KiranGunathilaka/gaurdian-call-IoT/Assets/OtherImages/20240525_033147.jpg

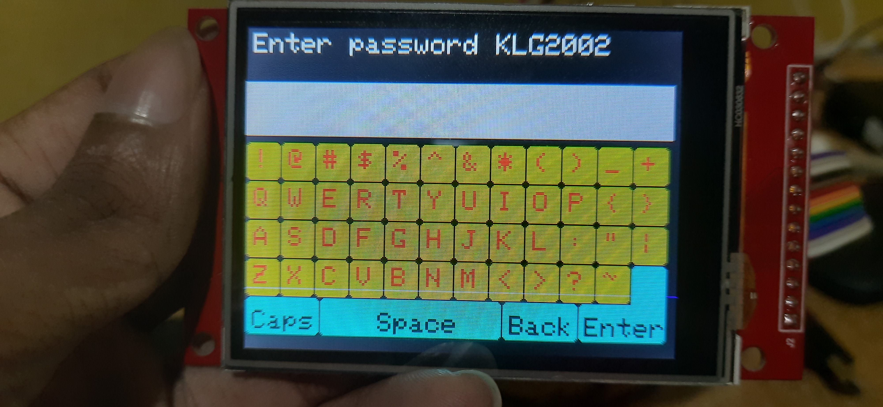
Assets/OtherImages/20240525_033147.jpg
