KiranGunathilaka/gaurdian-call-IoT/Assets/OtherImages/20240525_033200.jpg

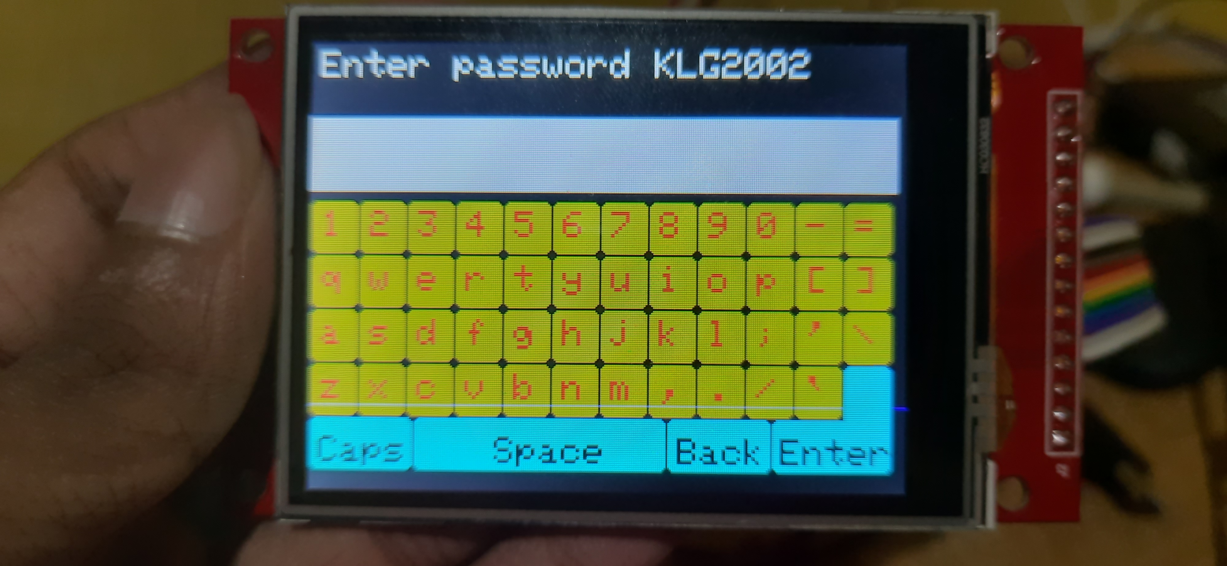
Assets/OtherImages/20240525_033200.jpg
