KiranGunathilaka/gaurdian-call-IoT/Assets/OtherImages/20240613_105201.jpg

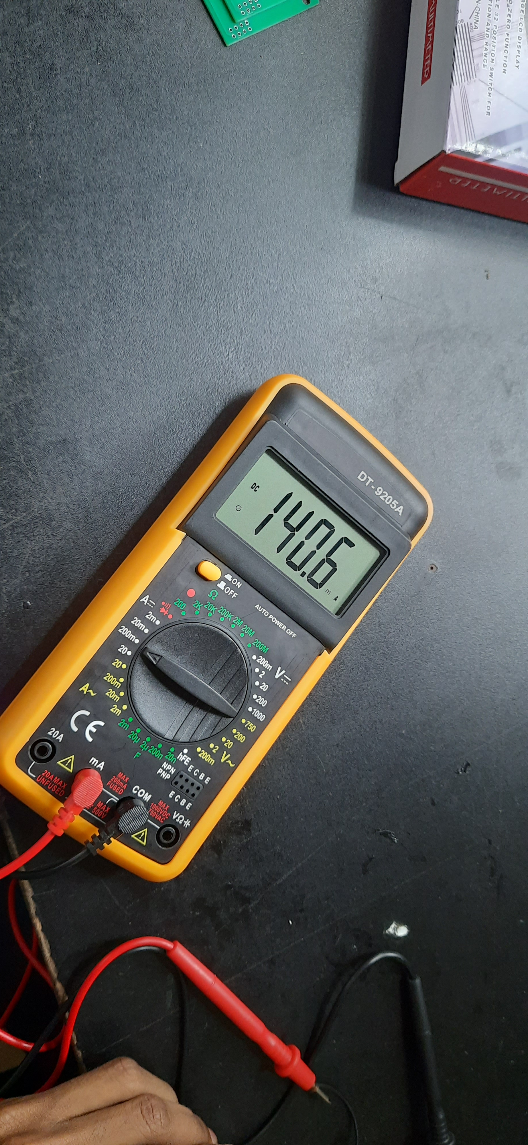
Assets/OtherImages/20240613_105201.jpg
