KiranGunathilaka/gaurdian-call-IoT/Assets/OtherImages/20240613_105238.jpg

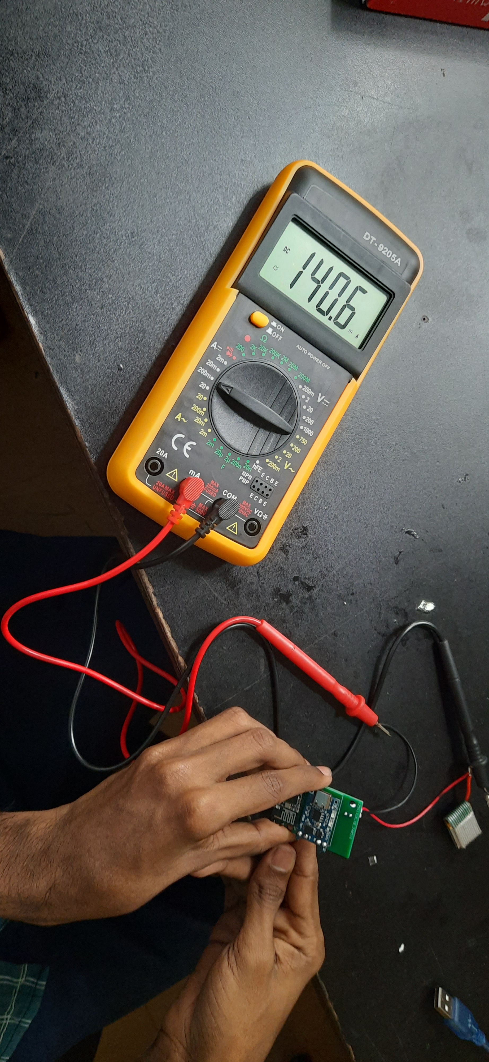
Assets/OtherImages/20240613_105238.jpg
