KiranGunathilaka/gaurdian-call-IoT/Assets/OtherImages/20240613_105256.jpg

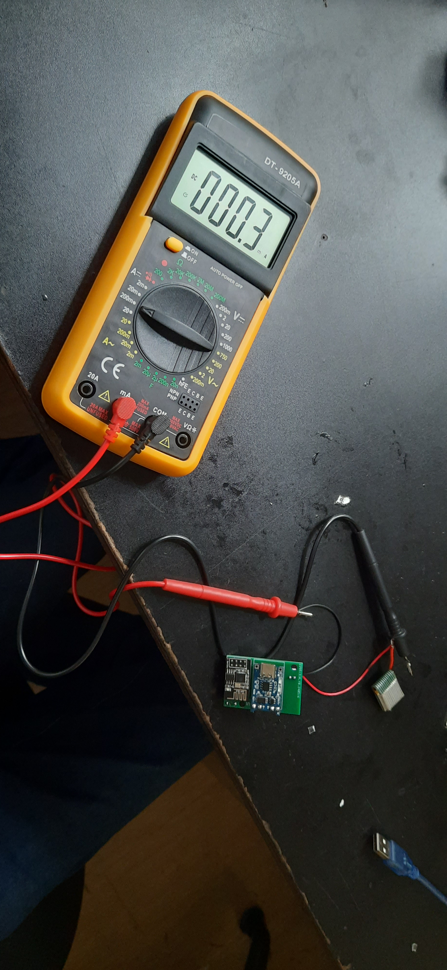
Assets/OtherImages/20240613_105256.jpg
