KiranGunathilaka/gaurdian-call-IoT/Assets/OtherImages/20240613_105300.jpg

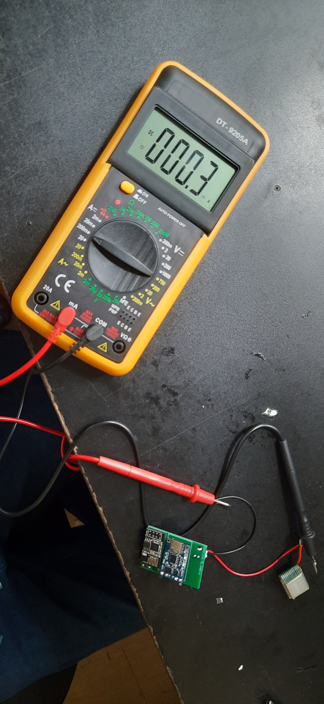
Assets/OtherImages/20240613_105300.jpg
