KiranGunathilaka/gaurdian-call-IoT/Assets/OtherImages/20240613_173540.jpg

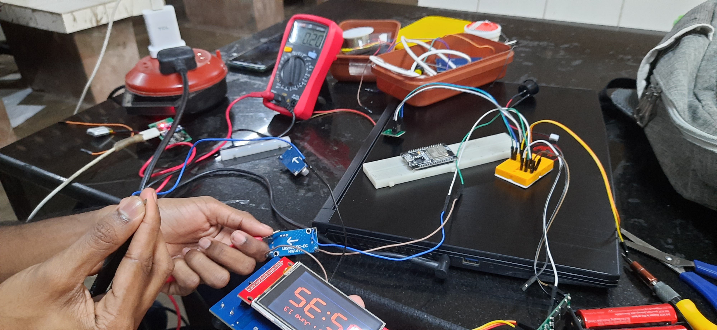
Assets/OtherImages/20240613_173540.jpg
