KiranGunathilaka/gaurdian-call-IoT/Assets/OtherImages/20240613_173549.jpg

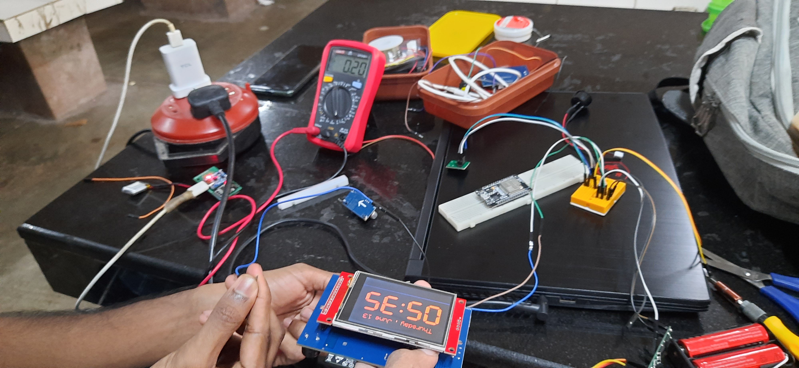
Assets/OtherImages/20240613_173549.jpg
