KiranGunathilaka/gaurdian-call-IoT/Assets/OtherImages/20240614_130550.jpg

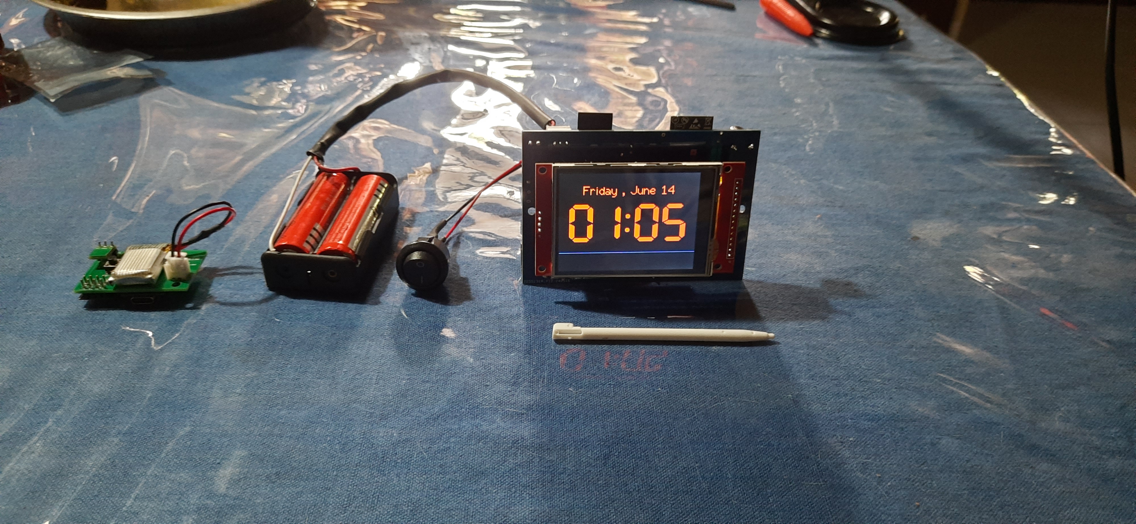
Assets/OtherImages/20240614_130550.jpg
