KiranGunathilaka/gaurdian-call-IoT/Assets/OtherImages/20240614_130608.jpg

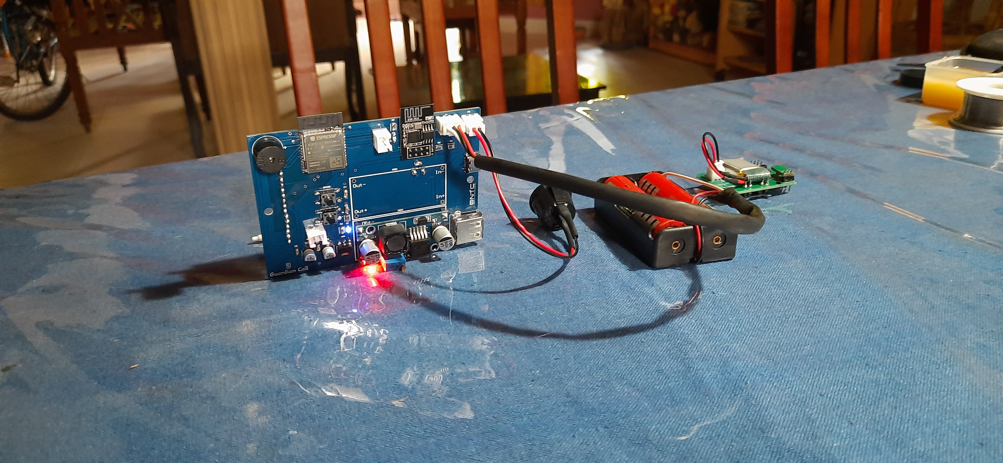
Assets/OtherImages/20240614_130608.jpg
