KiranGunathilaka/gaurdian-call-IoT/Assets/OtherImages/20240614_203509.jpg

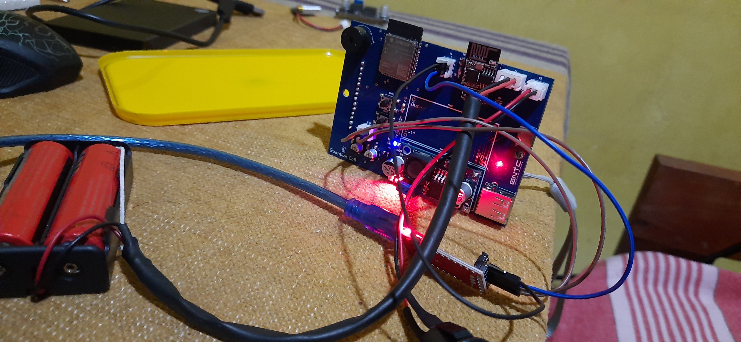
Assets/OtherImages/20240614_203509.jpg
