KiranGunathilaka/gaurdian-call-IoT/Assets/OtherImages/20240614_231927.jpg

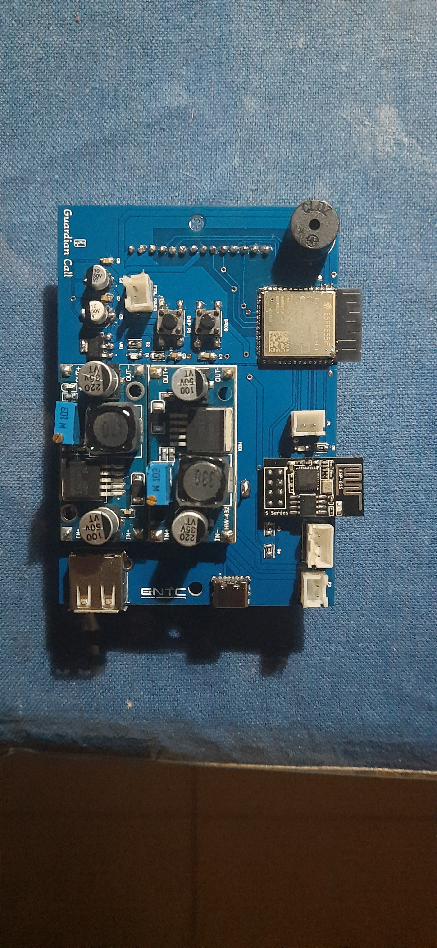
Assets/OtherImages/20240614_231927.jpg
