KiranGunathilaka/gaurdian-call-IoT/Assets/OtherImages/20240614_232202.jpg

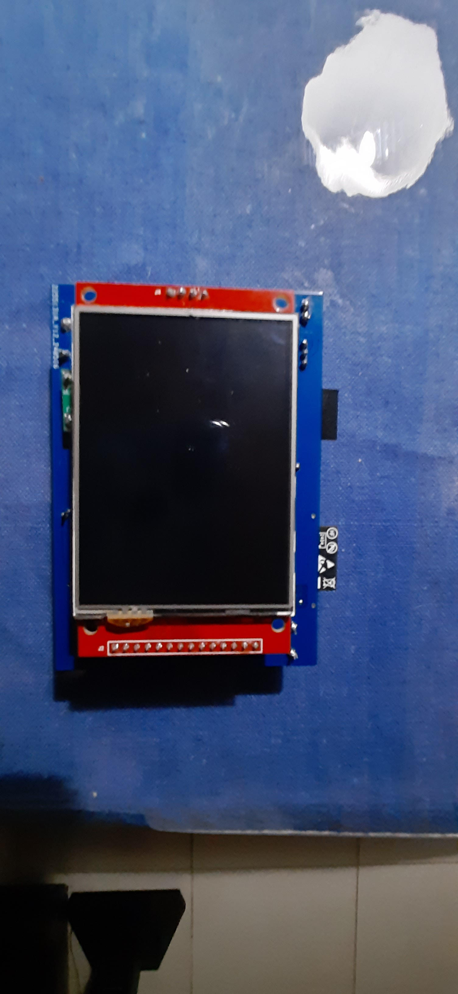
Assets/OtherImages/20240614_232202.jpg
