KiranGunathilaka/gaurdian-call-IoT/Assets/OtherImages/20240614_232258.jpg

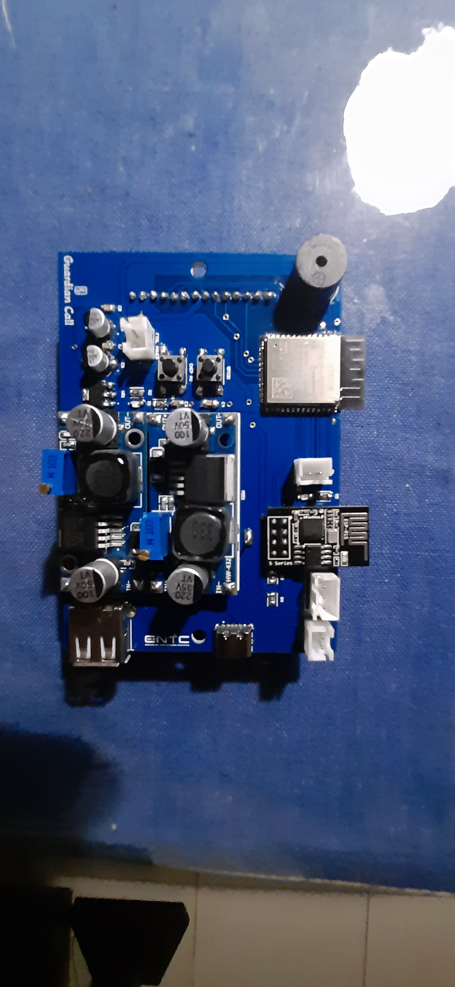
Assets/OtherImages/20240614_232258.jpg
