KiranGunathilaka/gaurdian-call-IoT/Assets/OtherImages/20240614_232338.jpg

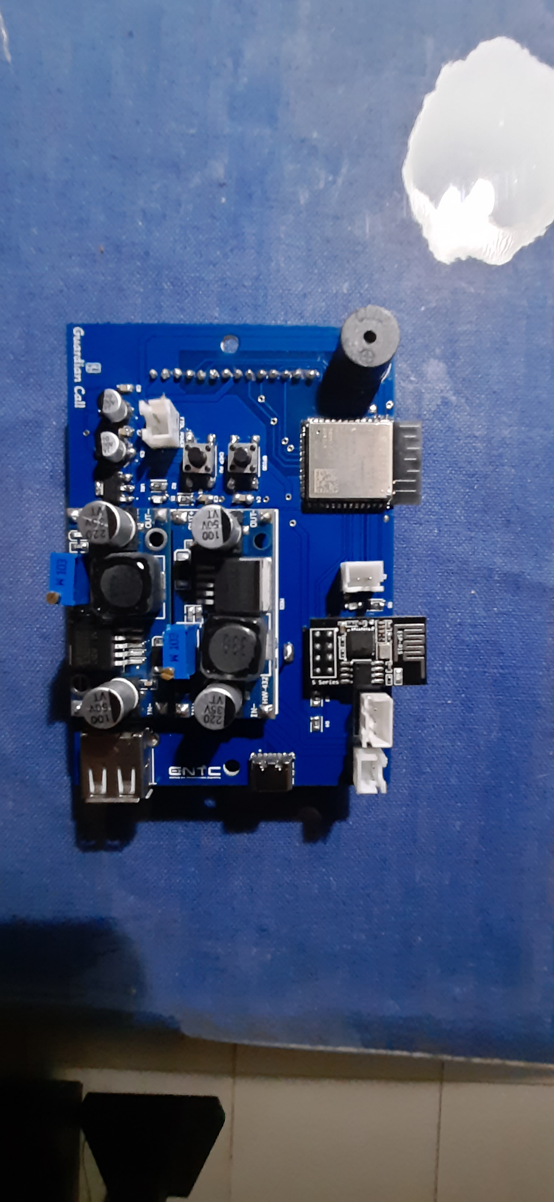
Assets/OtherImages/20240614_232338.jpg
