KiranGunathilaka/gaurdian-call-IoT/Assets/OtherImages/20240614_232511.jpg

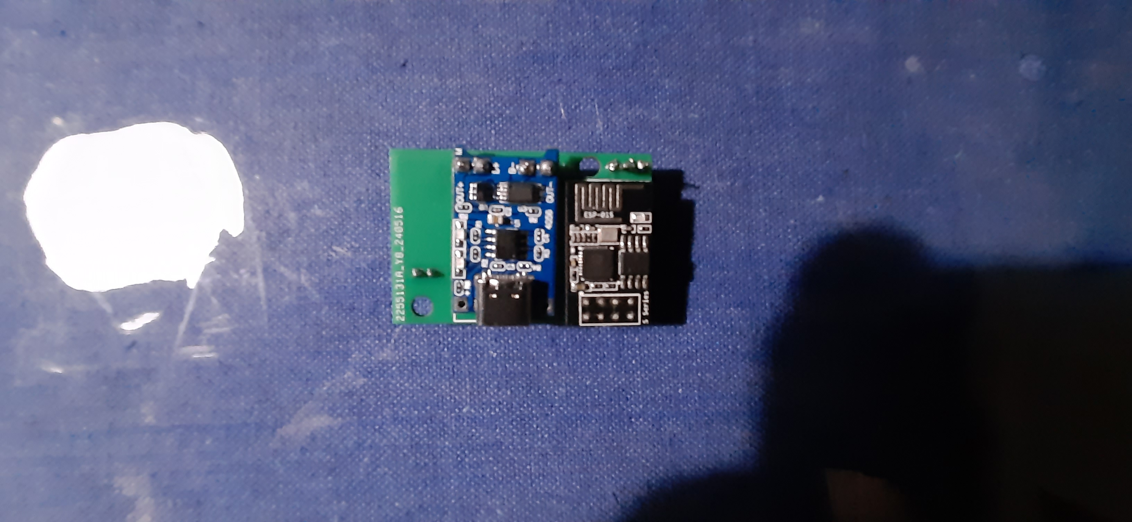
Assets/OtherImages/20240614_232511.jpg
