KiranGunathilaka/gaurdian-call-IoT/Assets/OtherImages/20240614_232523.jpg

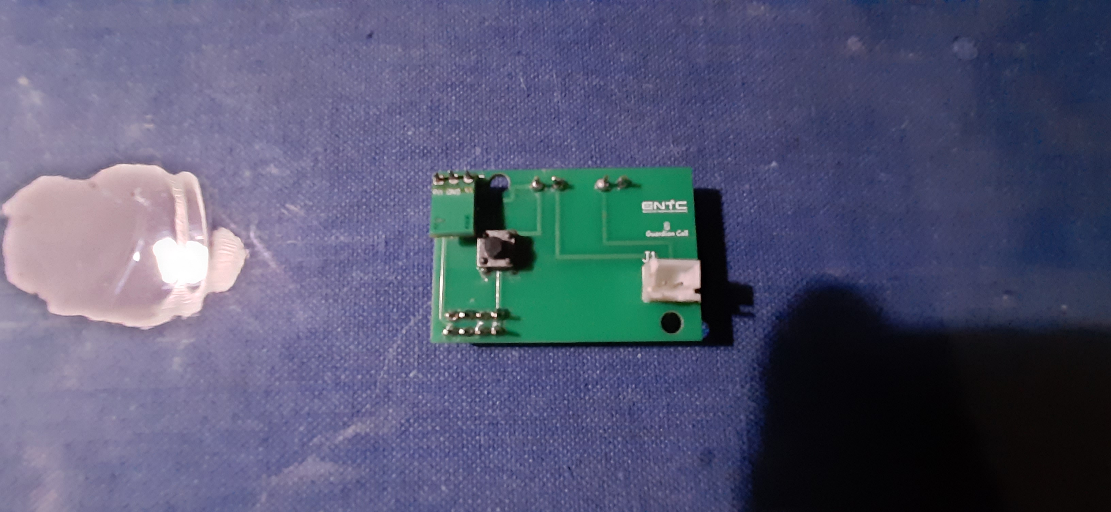
Assets/OtherImages/20240614_232523.jpg
