KiranGunathilaka/gaurdian-call-IoT/Assets/OtherImages/20240614_232553.jpg

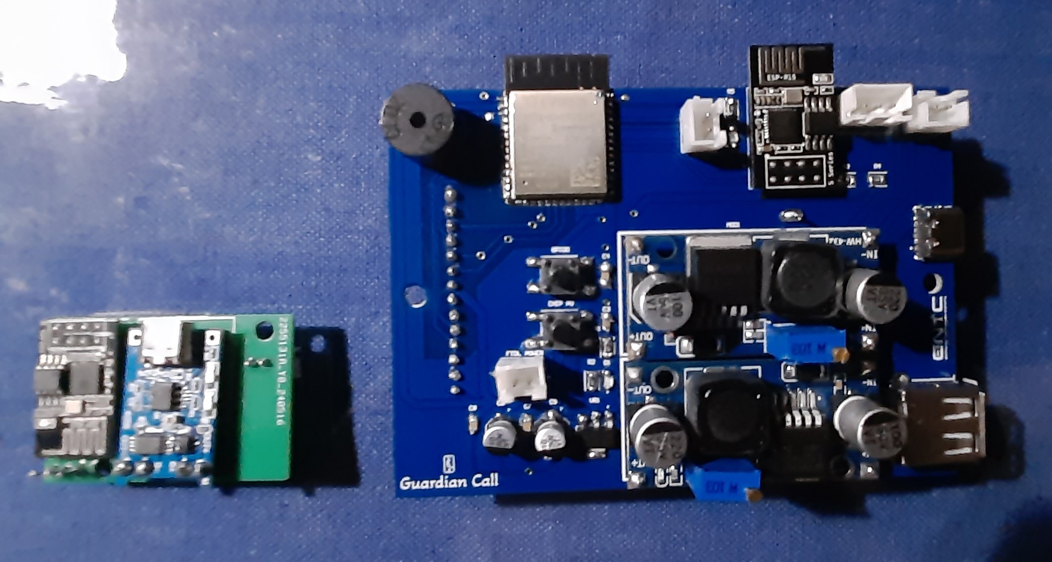
Assets/OtherImages/20240614_232553.jpg
