KiranGunathilaka/gaurdian-call-IoT/Assets/OtherImages/20240614_232625.jpg

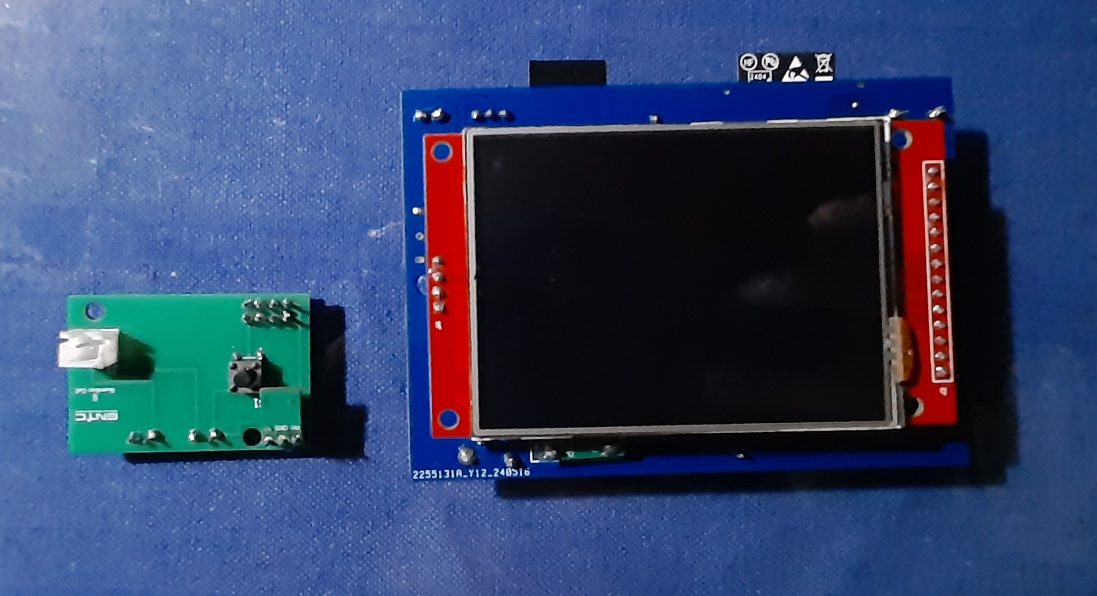
Assets/OtherImages/20240614_232625.jpg
