KiranGunathilaka/gaurdian-call-IoT/Assets/OtherImages/20240630_153155.jpg

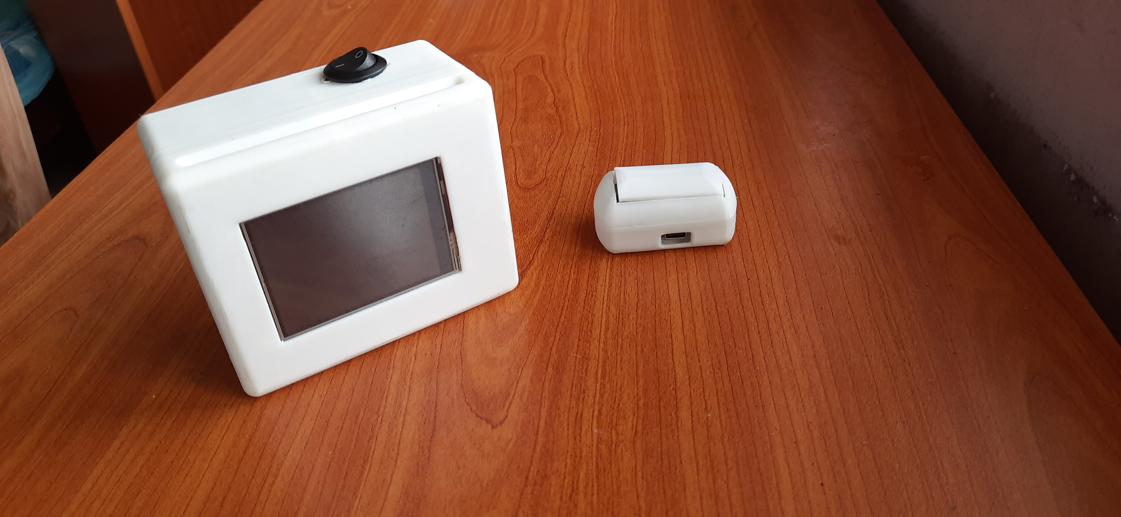
Assets/OtherImages/20240630_153155.jpg
