KiranGunathilaka/gaurdian-call-IoT/Assets/OtherImages/20240630_153201.jpg

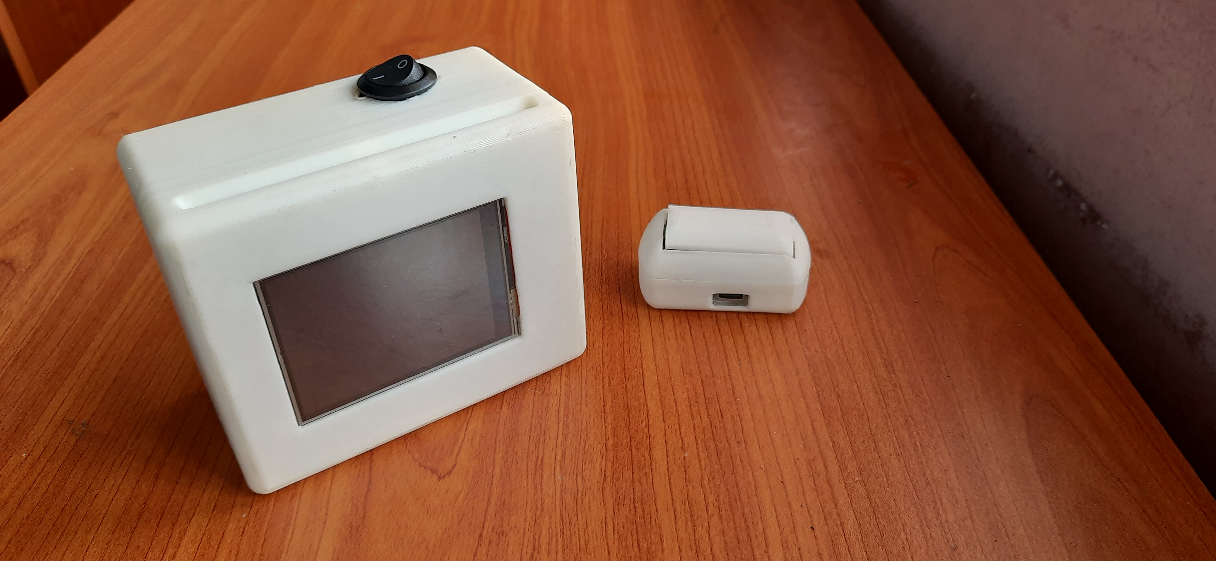
Assets/OtherImages/20240630_153201.jpg
