KiranGunathilaka/gaurdian-call-IoT/Assets/OtherImages/20240703_032037.jpg

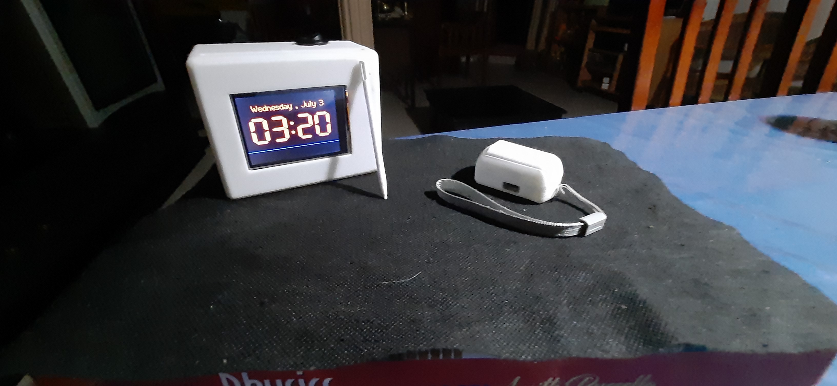
Assets/OtherImages/20240703_032037.jpg
