KiranGunathilaka/gaurdian-call-IoT/Assets/OtherImages/20240703_032049.jpg

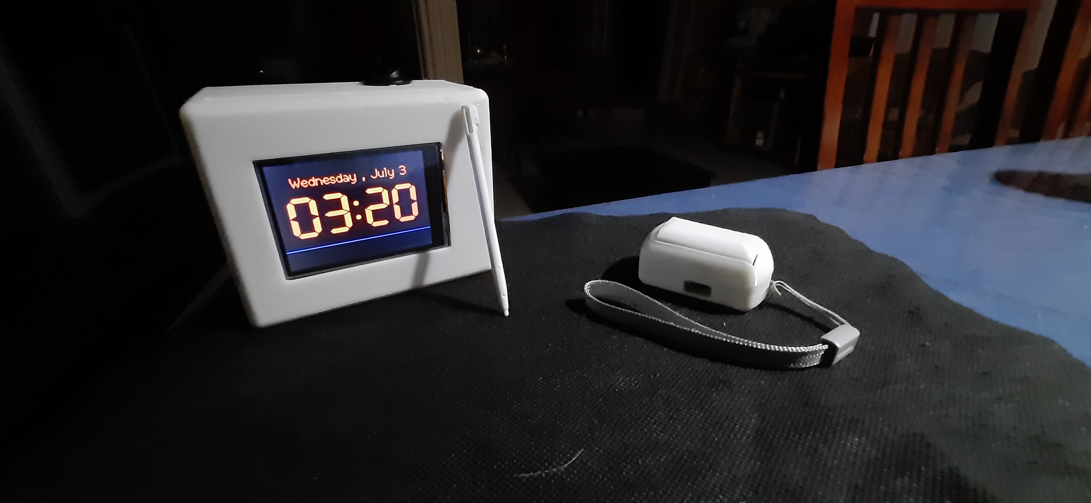
Assets/OtherImages/20240703_032049.jpg
