KiranGunathilaka/gaurdian-call-IoT/Assets/OtherImages/20240815_104027.jpg

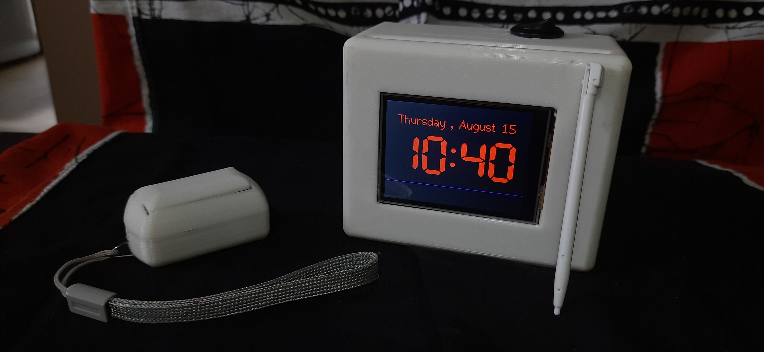
Assets/OtherImages/20240815_104027.jpg
