KiranGunathilaka/gaurdian-call-IoT/Assets/OtherImages/20240815_104038.jpg

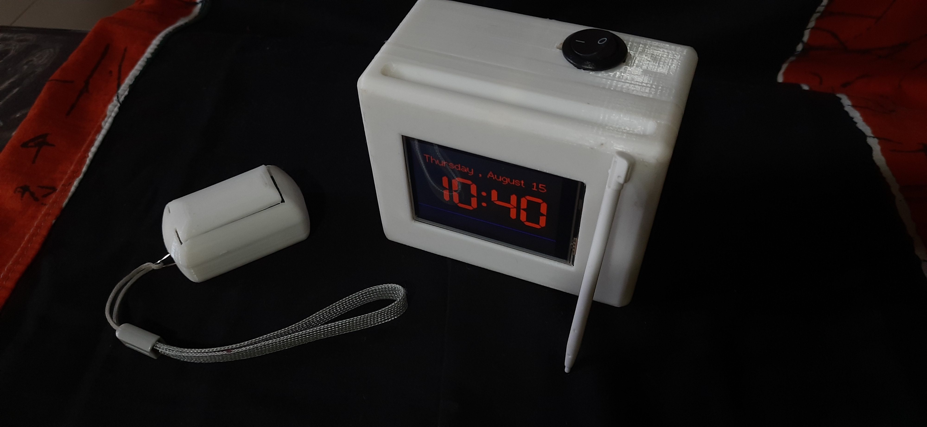
Assets/OtherImages/20240815_104038.jpg
