KiranGunathilaka/gaurdian-call-IoT/Assets/OtherImages/20240815_104104.jpg

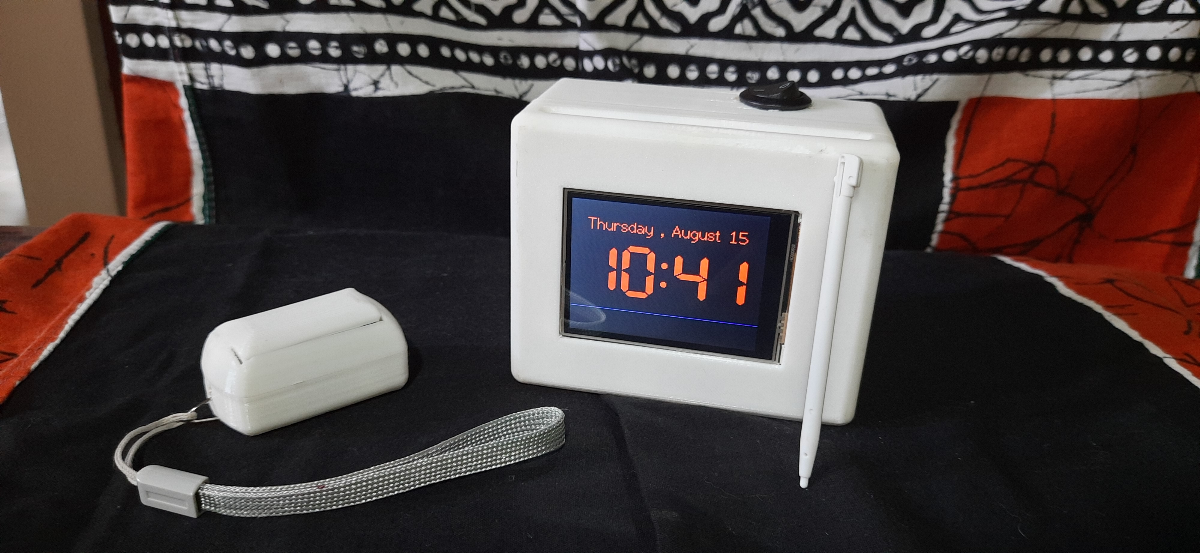
Assets/OtherImages/20240815_104104.jpg
