KiranGunathilaka/gaurdian-call-IoT/Assets/OtherImages/20240815_104159.jpg

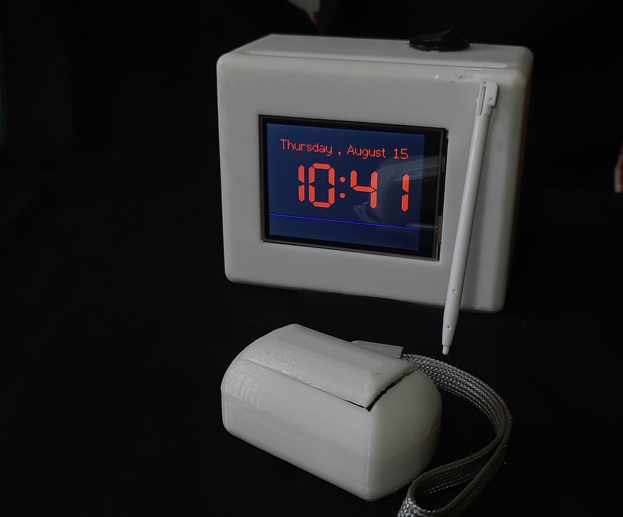
Assets/OtherImages/20240815_104159.jpg
