KiranGunathilaka/gaurdian-call-IoT/Assets/OtherImages/20240815_104340.jpg

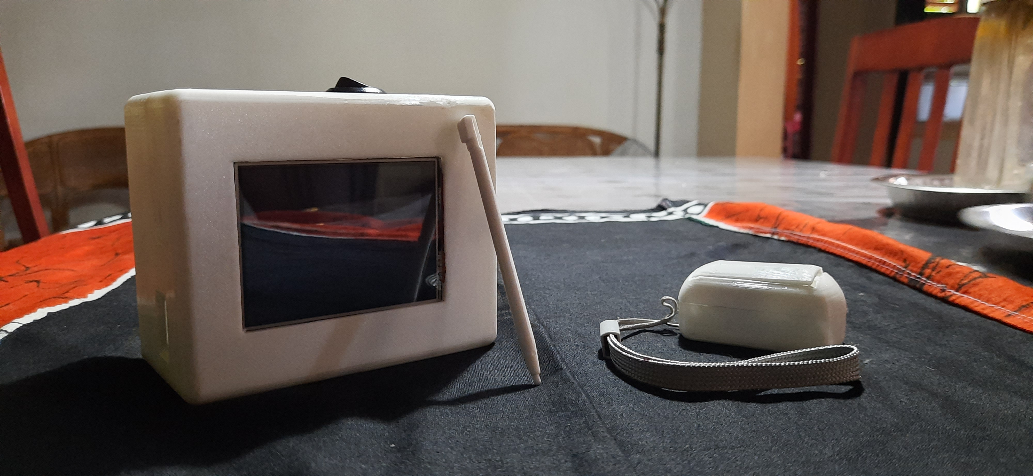
Assets/OtherImages/20240815_104340.jpg
