KiranGunathilaka/gaurdian-call-IoT/Assets/OtherImages/20240815_104405.jpg

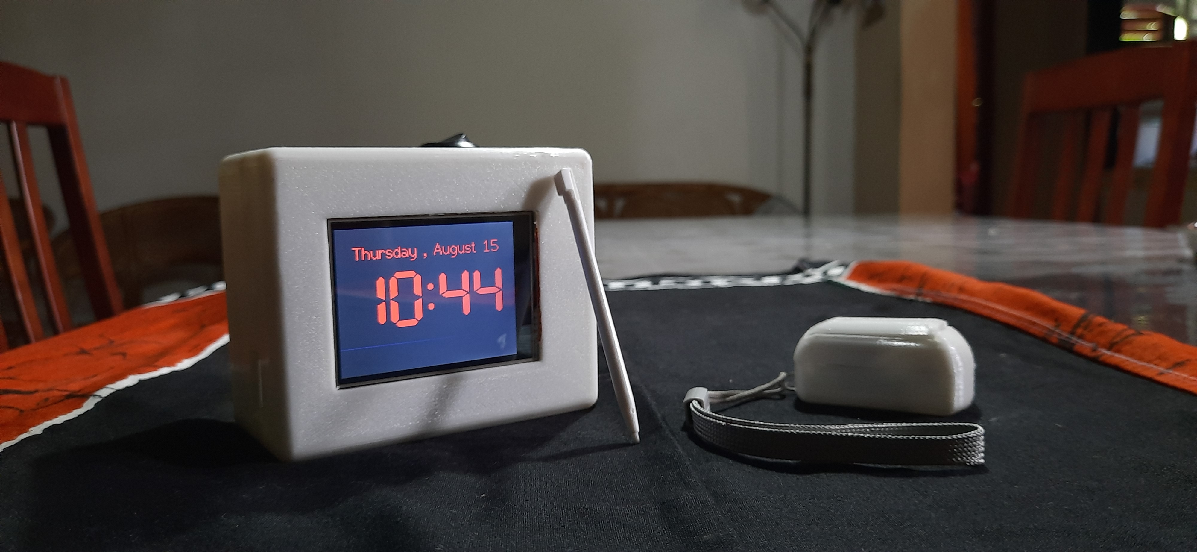
Assets/OtherImages/20240815_104405.jpg
