KiranGunathilaka/gaurdian-call-IoT/Assets/OtherImages/20240815_104449.jpg

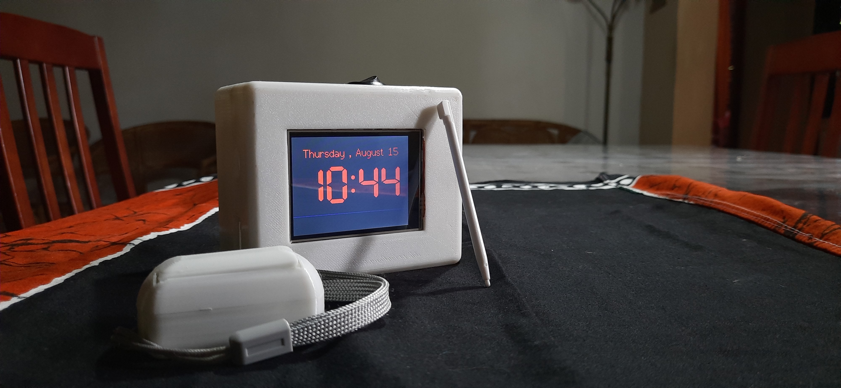
Assets/OtherImages/20240815_104449.jpg
