KiranGunathilaka/gaurdian-call-IoT/Assets/OtherImages/20240815_104604.jpg

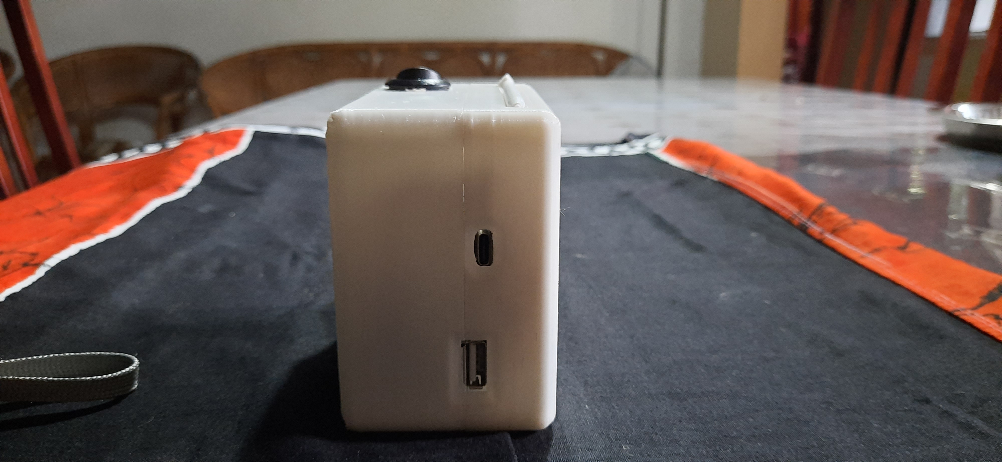
Assets/OtherImages/20240815_104604.jpg
