KiranGunathilaka/gaurdian-call-IoT/Assets/OtherImages/20240815_104700.jpg

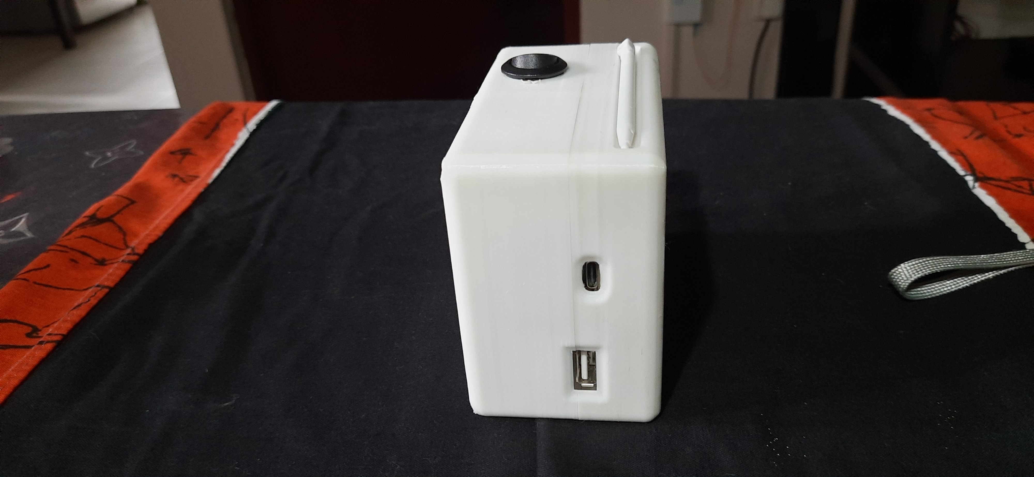
Assets/OtherImages/20240815_104700.jpg
