KiranGunathilaka/gaurdian-call-IoT/Assets/OtherImages/20240815_104720.jpg

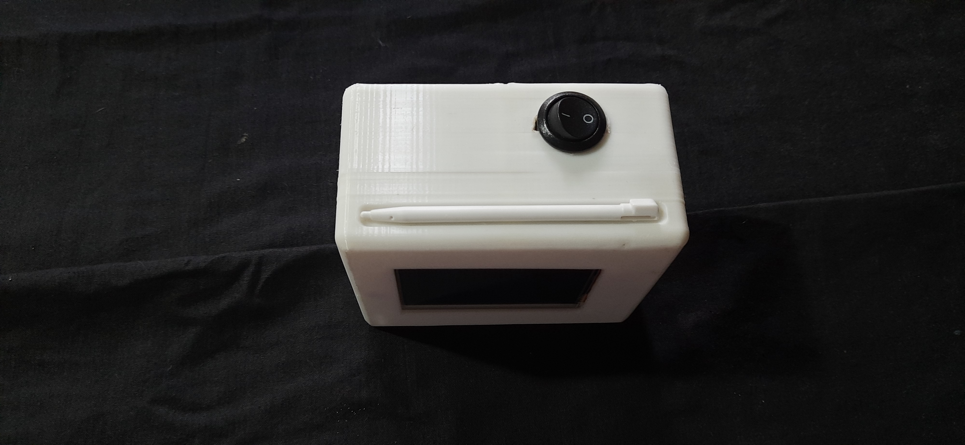
Assets/OtherImages/20240815_104720.jpg
