KiranGunathilaka/gaurdian-call-IoT/Assets/OtherImages/20240815_122412.jpg

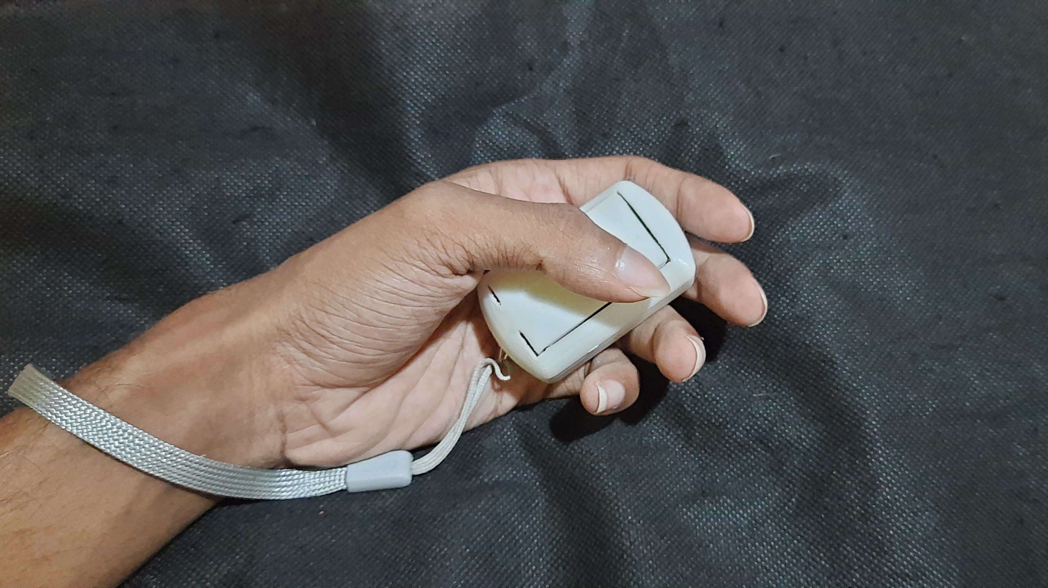
Assets/OtherImages/20240815_122412.jpg
