KiranGunathilaka/gaurdian-call-IoT/Assets/OtherImages/20240815_122552.jpg

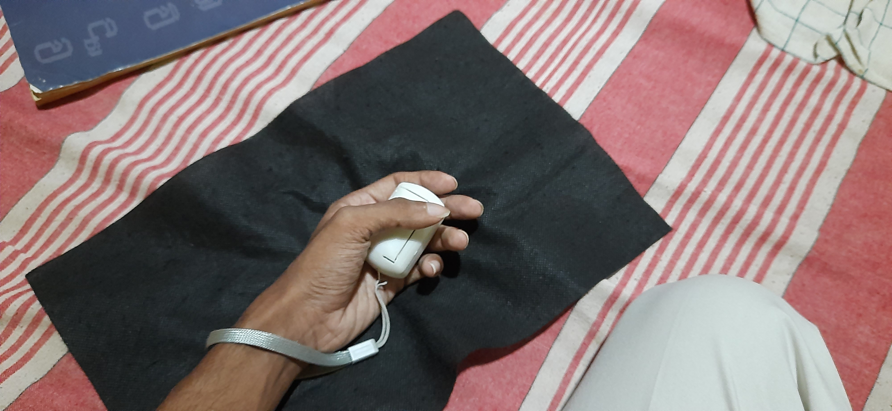
Assets/OtherImages/20240815_122552.jpg
