KiranGunathilaka/gaurdian-call-IoT/Assets/OtherImages/20240815_123546.jpg

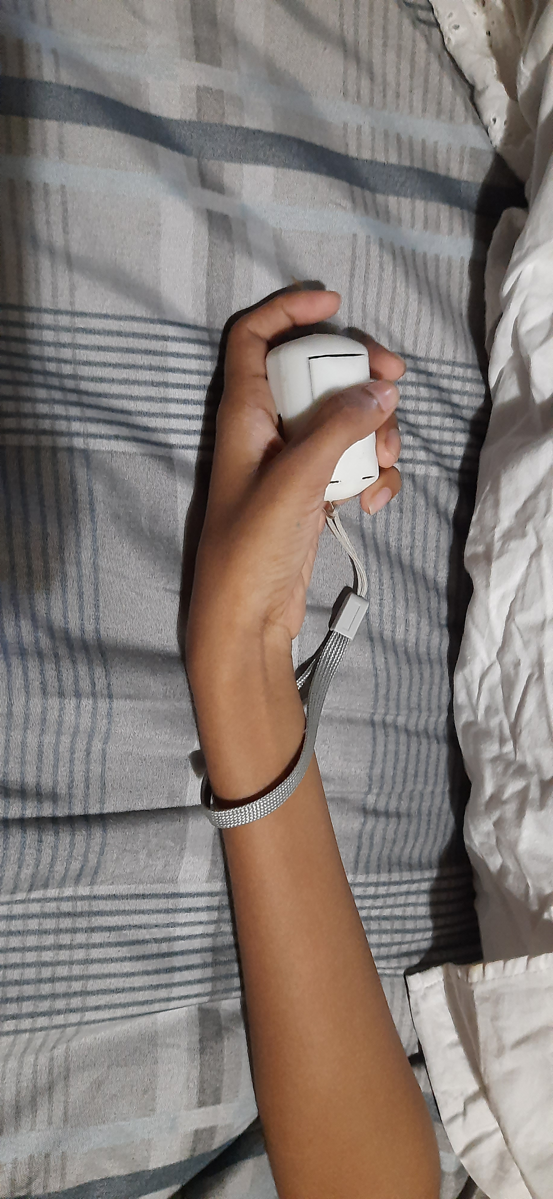
Assets/OtherImages/20240815_123546.jpg
