KiranGunathilaka/gaurdian-call-IoT/Assets/OtherImages/20240815_124415.jpg

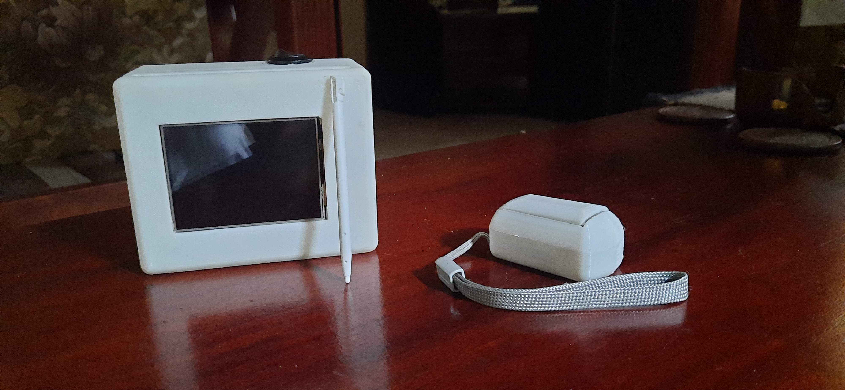
Assets/OtherImages/20240815_124415.jpg
