KiranGunathilaka/gaurdian-call-IoT/Assets/OtherImages/20240815_124422.jpg

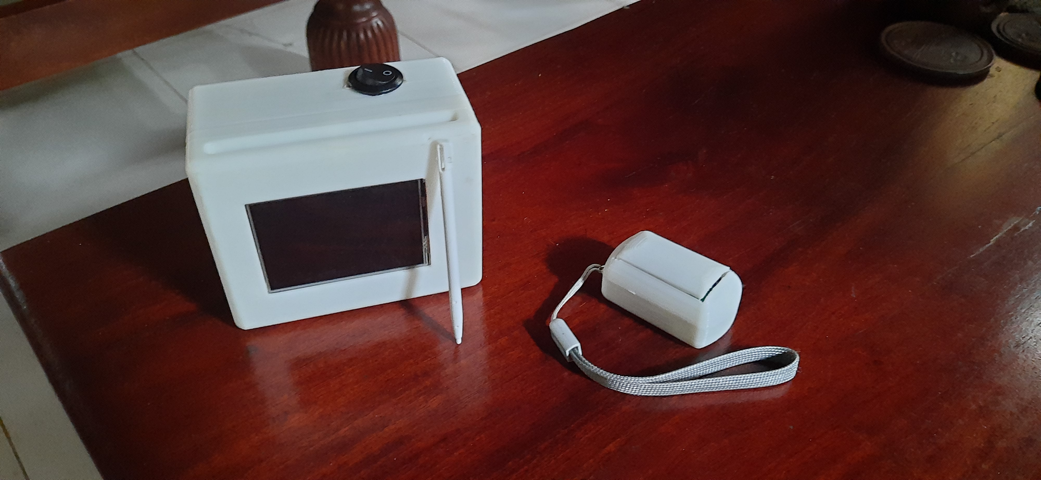
Assets/OtherImages/20240815_124422.jpg
