KiranGunathilaka/gaurdian-call-IoT/Assets/OtherImages/20240815_124434.jpg

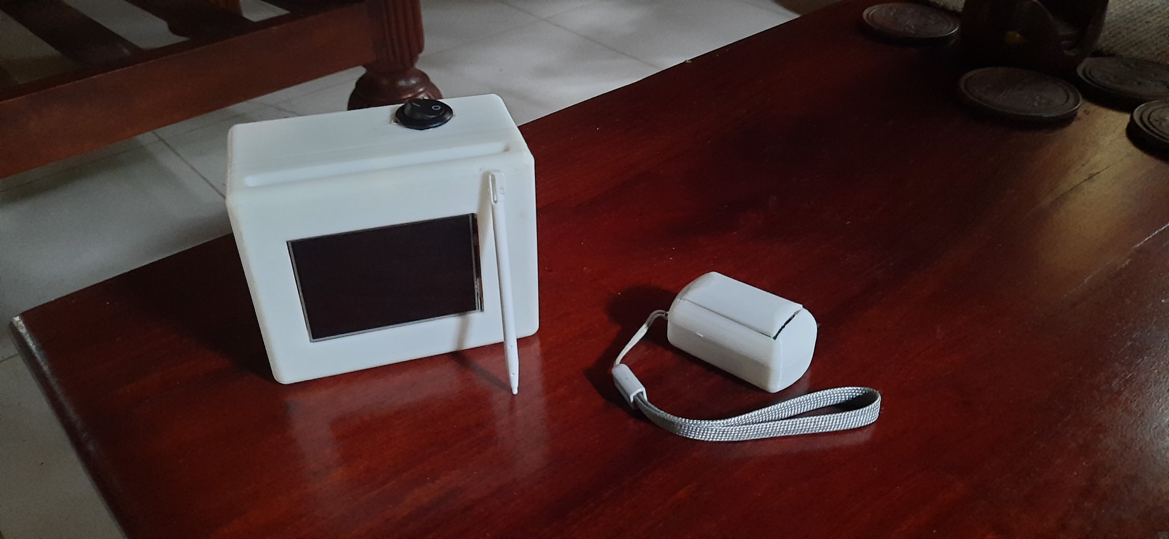
Assets/OtherImages/20240815_124434.jpg
