KiranGunathilaka/gaurdian-call-IoT/Assets/OtherImages/20240815_124450.jpg

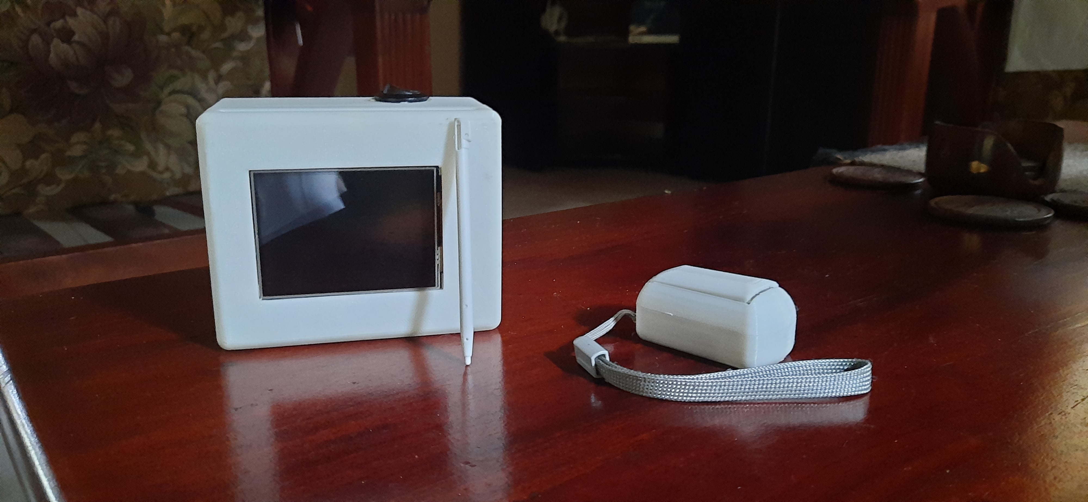
Assets/OtherImages/20240815_124450.jpg
