KiranGunathilaka/gaurdian-call-IoT/Assets/OtherImages/20240815_124516.jpg

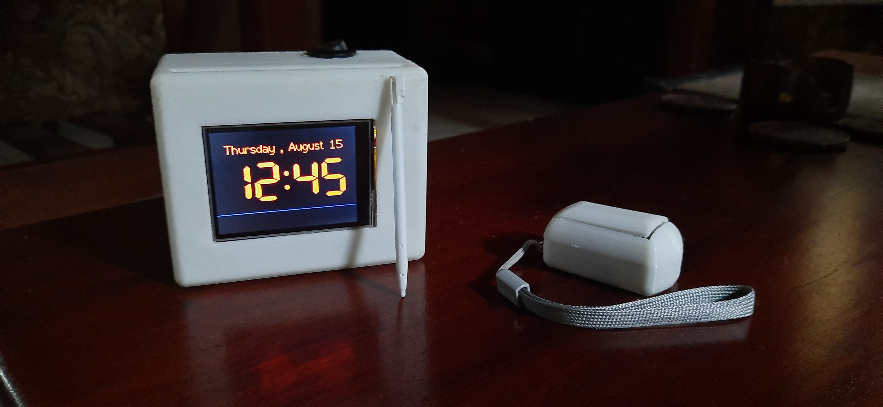
Assets/OtherImages/20240815_124516.jpg
