KiranGunathilaka/gaurdian-call-IoT/Assets/OtherImages/20240815_124621.jpg

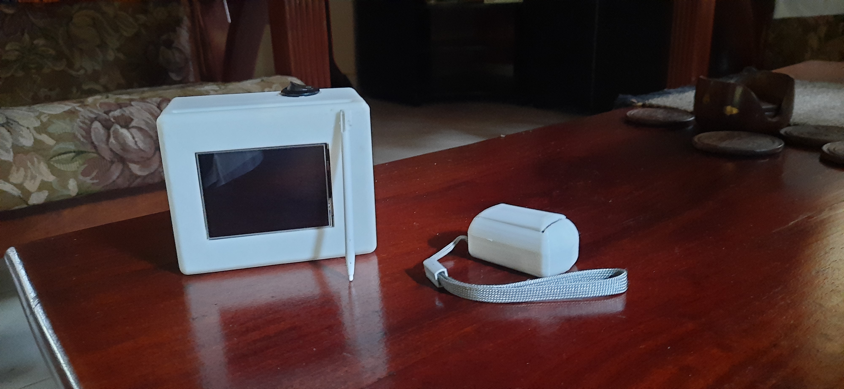
Assets/OtherImages/20240815_124621.jpg
