KiranGunathilaka/gaurdian-call-IoT/Assets/OtherImages/20240815_124631.jpg

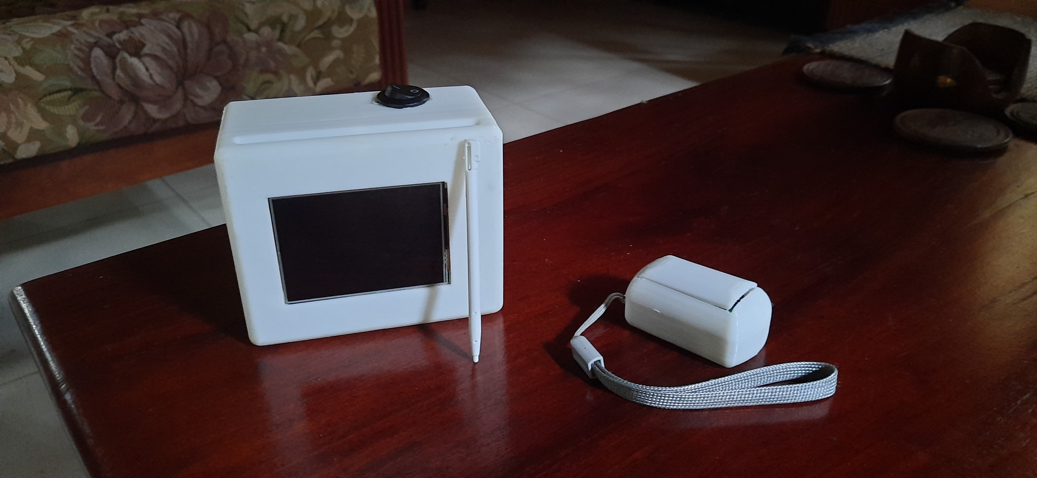
Assets/OtherImages/20240815_124631.jpg
