KiranGunathilaka/gaurdian-call-IoT/Assets/OtherImages/20240831_091419.jpg

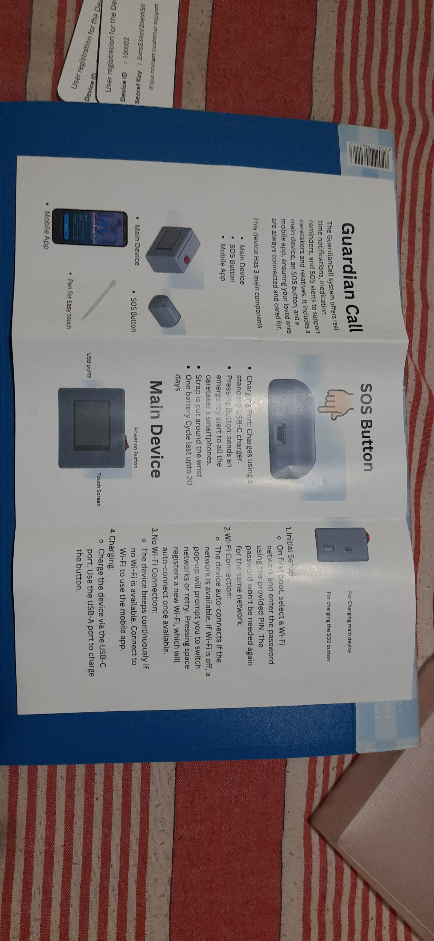
Assets/OtherImages/20240831_091419.jpg
