KiranGunathilaka/gaurdian-call-IoT/Assets/OtherImages/20240831_091440.jpg

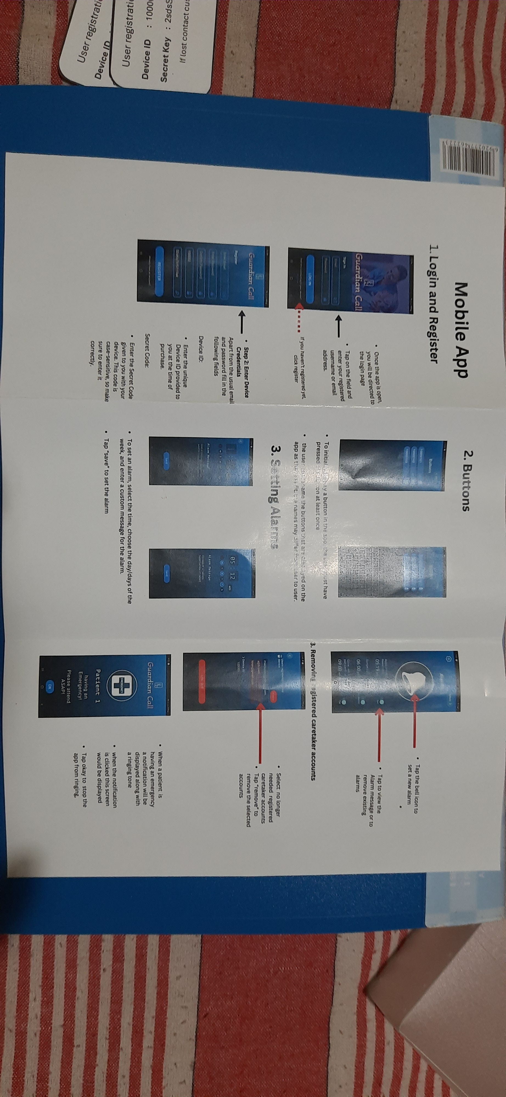
Assets/OtherImages/20240831_091440.jpg
