KiranGunathilaka/gaurdian-call-IoT/Assets/OtherImages/20240831_091508.jpg

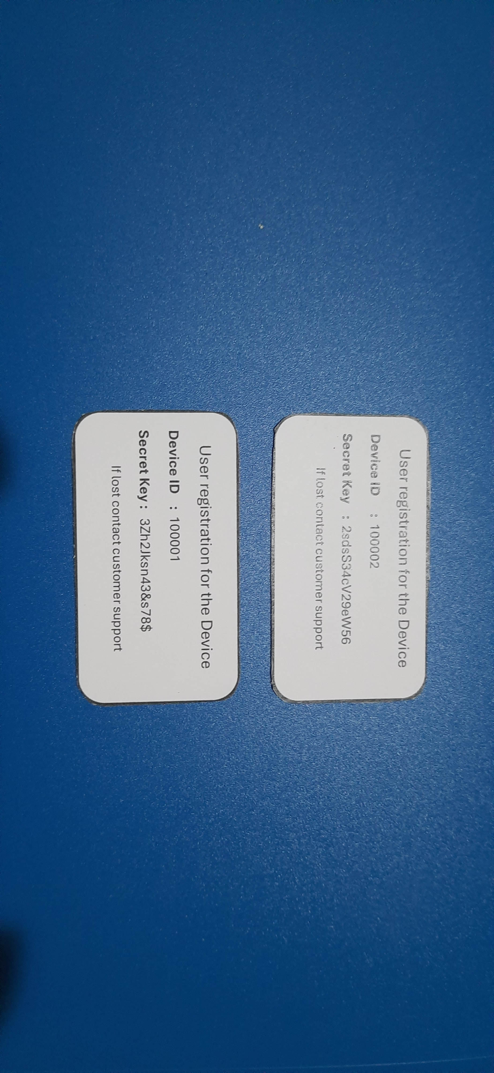
Assets/OtherImages/20240831_091508.jpg
